LunarKnights/SN65HVD257-breakout/can-breakout.pdf

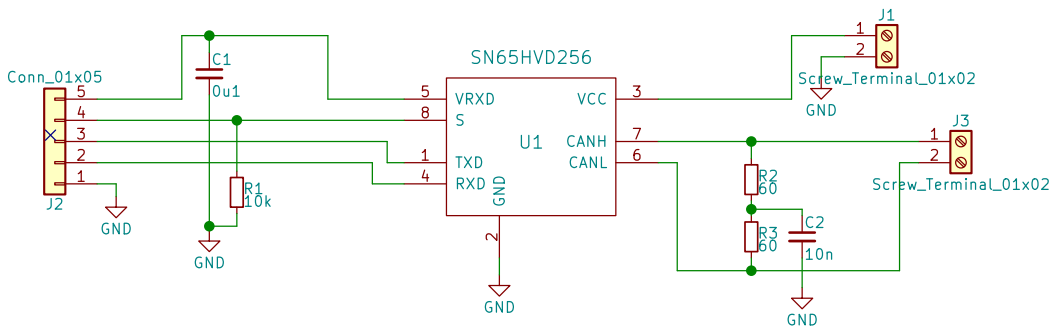
[picture p7: page 1]
